SnakeSolid/rust-stm32-temperature/bme280/src/lib.rs

#![no_std]

mod bme280;
mod humidity;
mod pressure;
mod temperature;

pub use crate::bme280::Bme280;
pub use crate::bme280::BmeStatus;
pub use crate::bme280::HumiditySampling;
pub use crate::bme280::PressureSampling;
pub use crate::bme280::SensorMode;
pub use crate::bme280::TemperatireSampling;
pub use crate::humidity::HumidityExt;
pub use crate::pressure::PressureExt;
pub use crate::temperature::TemperatureExt;
